Maltheren/Bilag-P2/Kicad filer/PowerAddOn/PowerAddOn/PowerAddOn2_Tekst.png

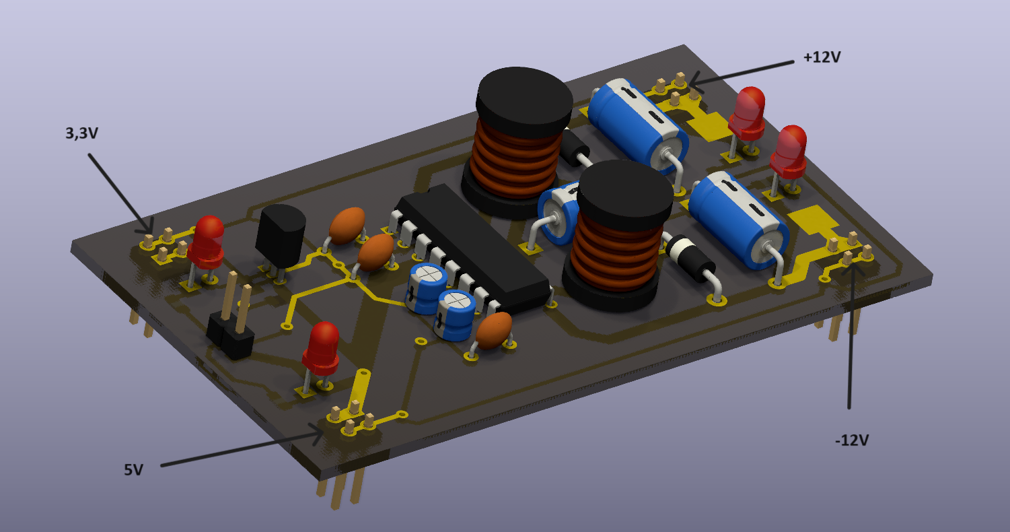
Kicad filer/PowerAddOn/PowerAddOn/PowerAddOn2_Tekst.png
