Maltheren/Bilag-P2/Kicad filer/PowerAddOn/PowerAddOn/PowerAddOn.png

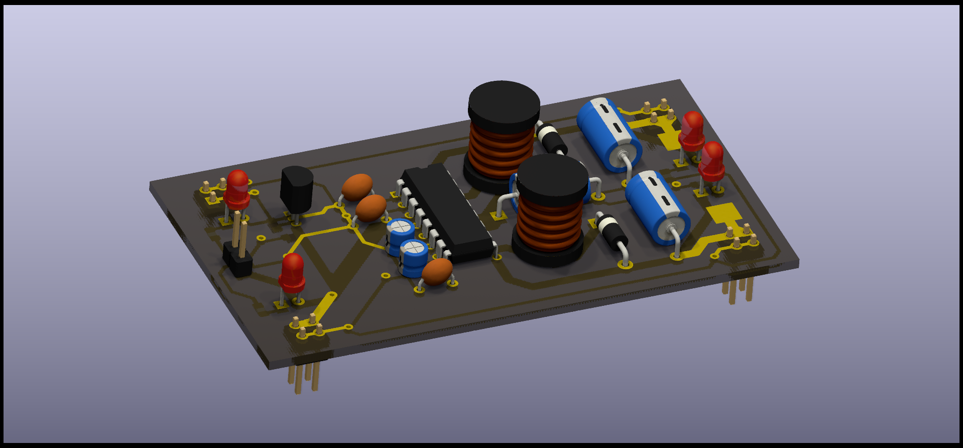
Kicad filer/PowerAddOn/PowerAddOn/PowerAddOn.png
