Maltheren/Bilag-P2/Kicad filer/PowerAddOn/PowerAddOn/PowerAddOn2.png

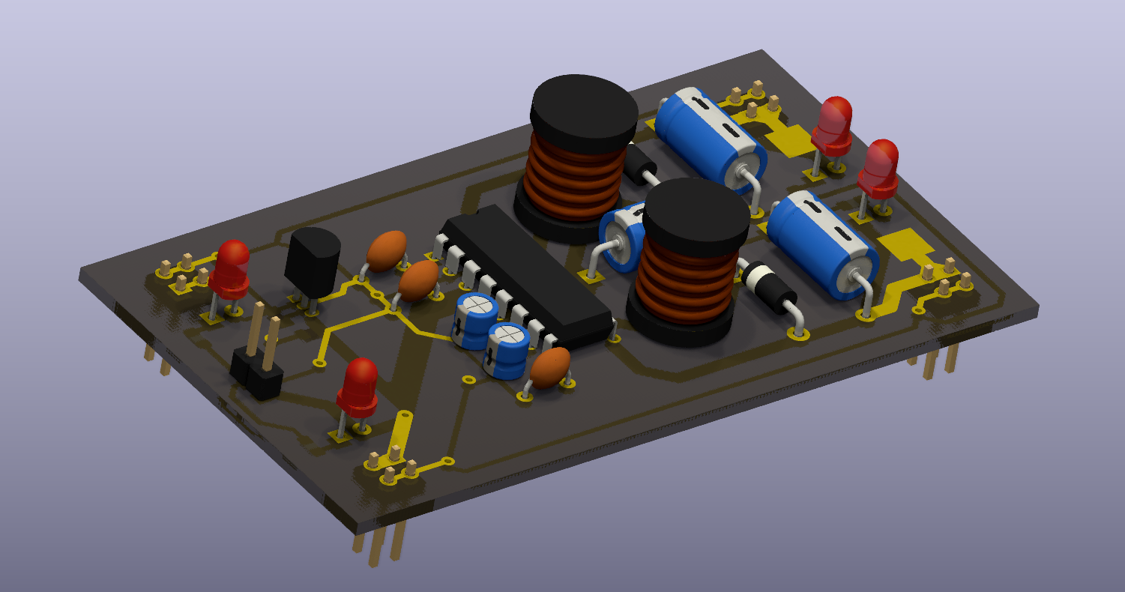
Kicad filer/PowerAddOn/PowerAddOn/PowerAddOn2.png
