Maltheren/Bilag-P2/Tests/Begge/S1 S2.csv

Frequency Log(Hz) | Gain (dB) | Phase (deg)
1.00010441154522 | -11.9575951670941 | -29.9110186335
1.02002096711708 | -10.968262479137 | -37.6873173948769
1.03995038360925 | -10.0583694415668 | -44.9132000611182
1.05985181982658 | -9.16374958422632 | -51.8982732066077
1.08009364755968 | -8.27616093757128 | -59.1885787538964
1.09981976674463 | -7.56683191751845 | -66.9312181141257
1.12016338353543 | -6.65872667450061 | -75.1817526079267
1.13994833382499 | -5.97810641974102 | -82.8378422791133
1.1598799011097 | -5.09345173903778 | -91.2556940941279
1.17990004057843 | -4.46642739230852 | -99.6509263969125
1.19995760707635 | -3.64138312726642 | -108.965429424205
1.22000782988254 | -3.14439374611364 | -117.749297890516
1.24001176959216 | -2.44859818749582 | -126.62713030138
1.25993577678249 | -1.8193012226693 | -136.34132482091
1.28000575955782 | -1.35183178602616 | -145.551987054429
1.29991959667752 | -0.882729519863348 | -155.262735367523
1.31989067760814 | -0.368316962118926 | -164.963904290659
1.34009406369643 | 0.000163560611546199 | -175.029001340476
1.36003523728506 | 0.295980291337435 | 175.345707751371
1.37991109385924 | 0.604438499301783 | 165.078606791357
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
