Maltheren/Bilag-P2/Tests/Begge/HelhedstestOpstilling.drawio.png

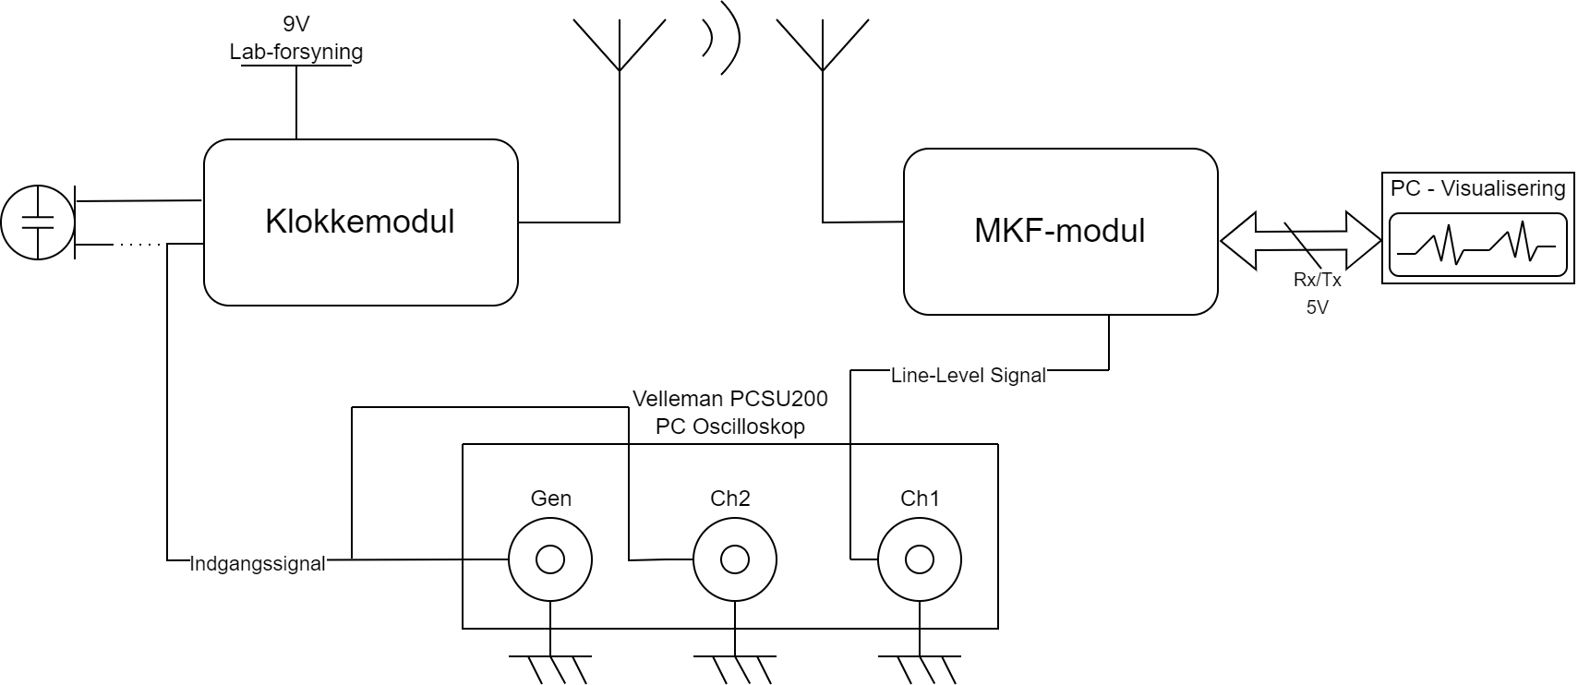
Tests/Begge/HelhedstestOpstilling.drawio.png
