Maltheren/Bilag-P2/Tests/Begge/HelhedstestOpstilling.png

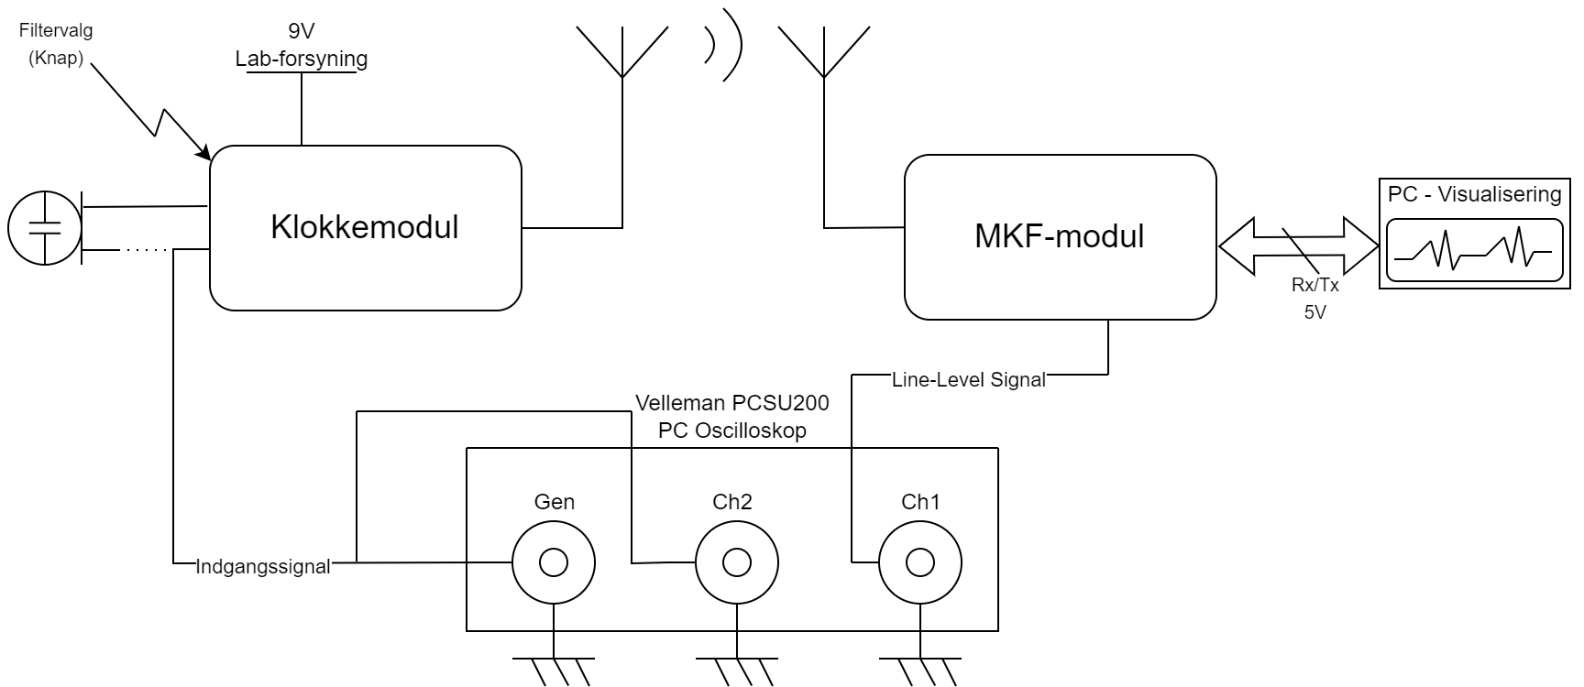
Tests/Begge/HelhedstestOpstilling.png
