Maltheren/Bilag-P2/Tests/Begge/Matlab/KlokkeOgRekon/Amplitude respons gengivelse.png

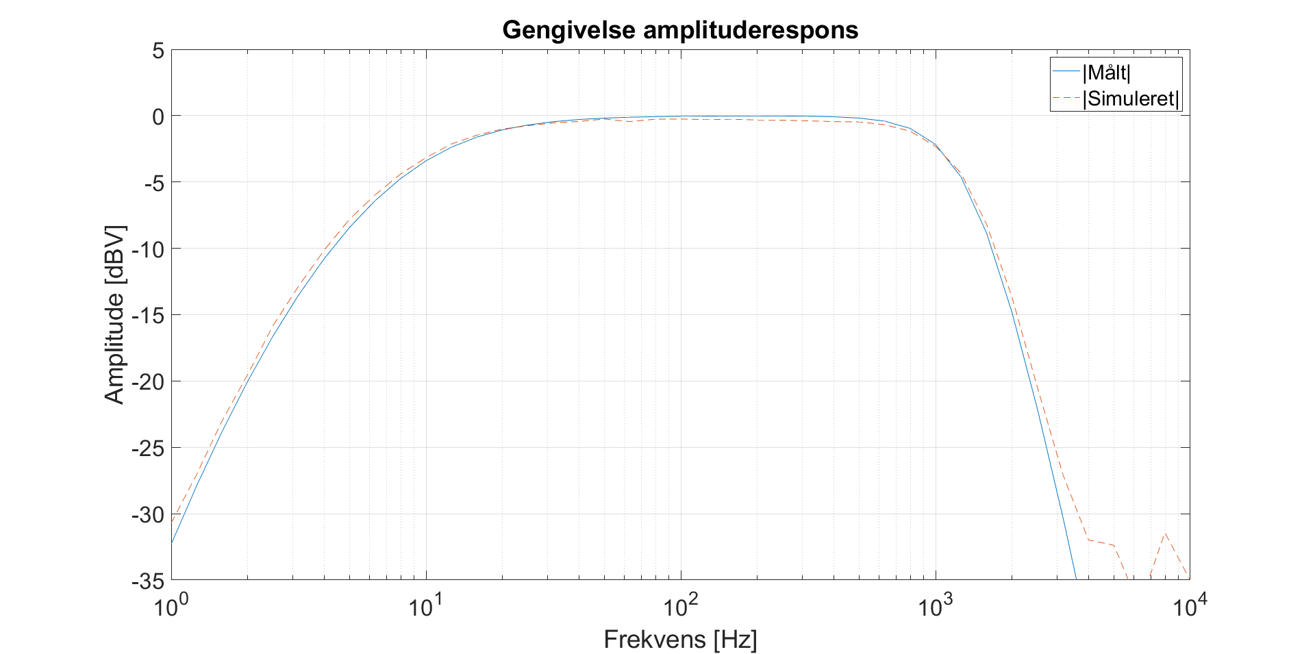
Tests/Begge/Matlab/KlokkeOgRekon/Amplitude respons gengivelse.png
