Maltheren/Bilag-P2/Tests/Begge/Matlab/KlokkeOgRekon/KlokkeOgRekon.jpg

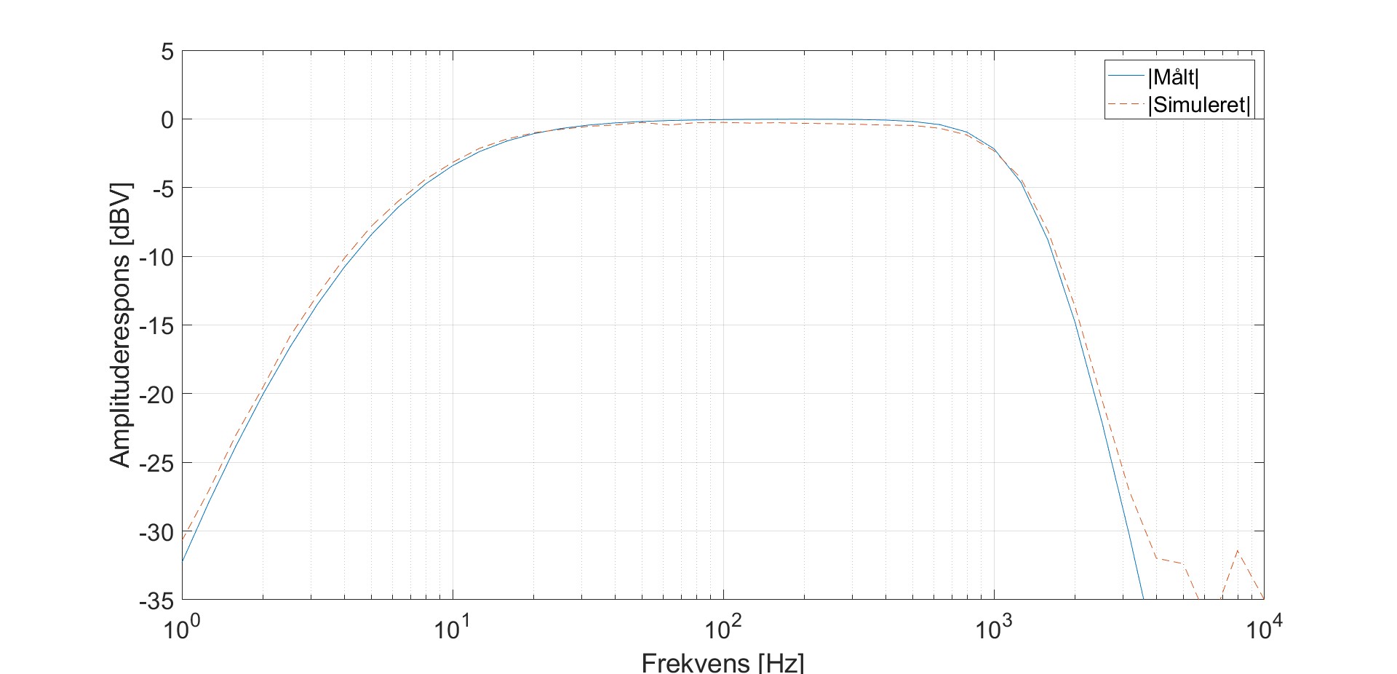
Tests/Begge/Matlab/KlokkeOgRekon/KlokkeOgRekon.jpg
