Maltheren/Bilag-P2/Tests/Begge/Matlab/Kvantisering/Billeder/Amplitude.png

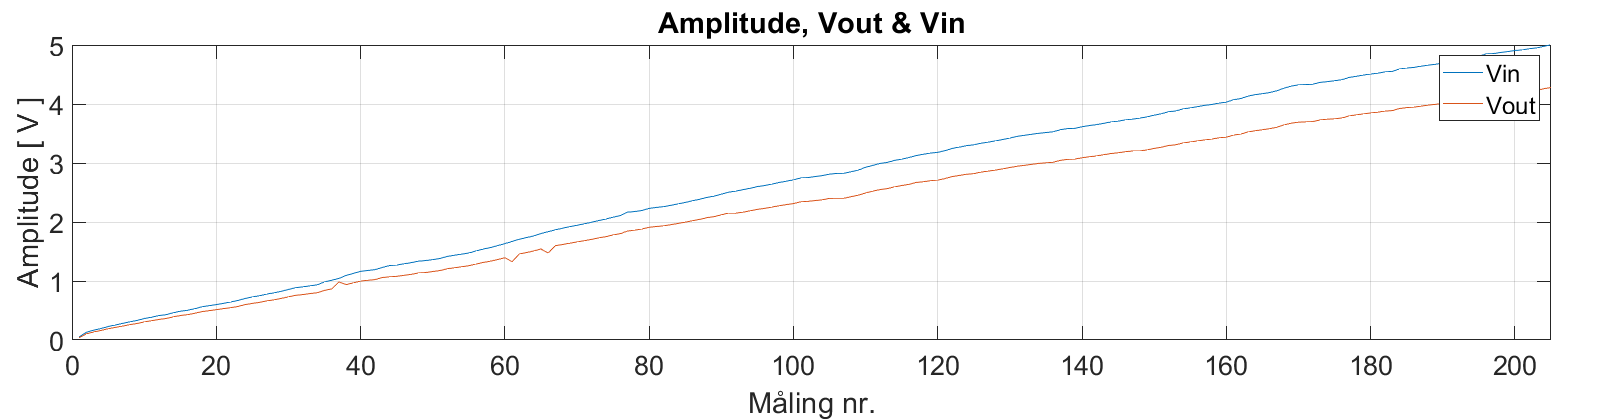
Tests/Begge/Matlab/Kvantisering/Billeder/Amplitude.png
