Maltheren/Bilag-P2/Tests/Begge/Matlab/Kvantisering/Billeder/Amplitude_VoutVin.jpg

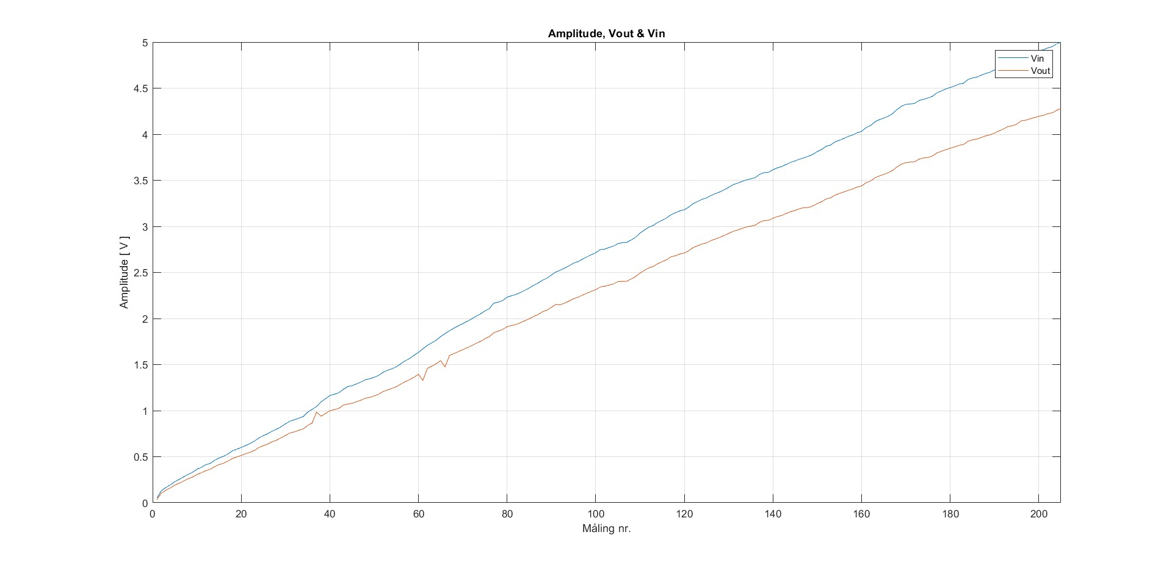
Tests/Begge/Matlab/Kvantisering/Billeder/Amplitude_VoutVin.jpg
