Maltheren/Bilag-P2/Tests/Begge/Matlab/Kvantisering/Billeder/Kvantiseringsfejl_Amplitude.jpg

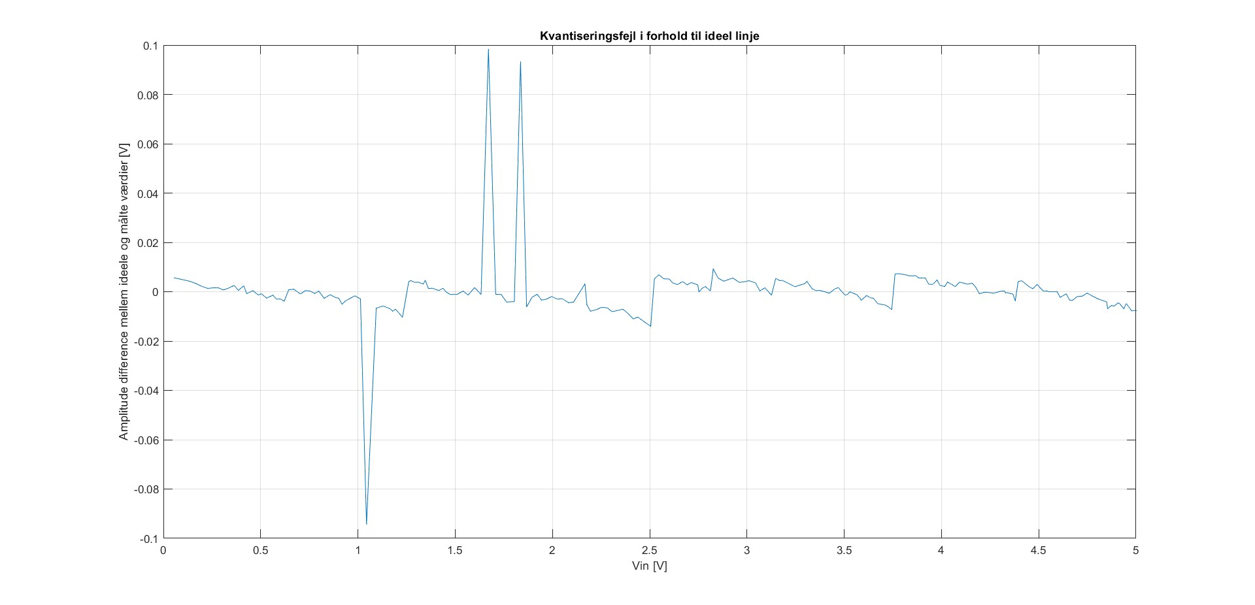
Tests/Begge/Matlab/Kvantisering/Billeder/Kvantiseringsfejl_Amplitude.jpg
