Maltheren/Bilag-P2/Tests/Begge/Matlab/Kvantisering/Billeder/Kvantiseringsfejl_ideel.png

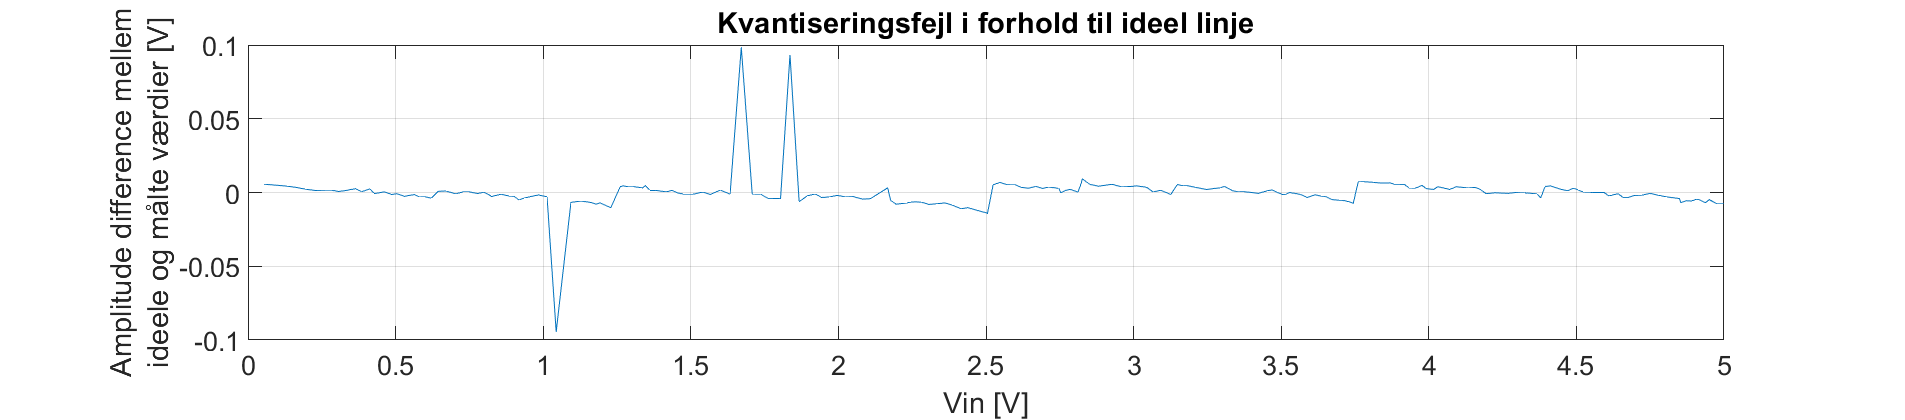
Tests/Begge/Matlab/Kvantisering/Billeder/Kvantiseringsfejl_ideel.png
