Maltheren/Bilag-P2/Tests/Begge/Matlab/Kvantisering/VinVout.jpg

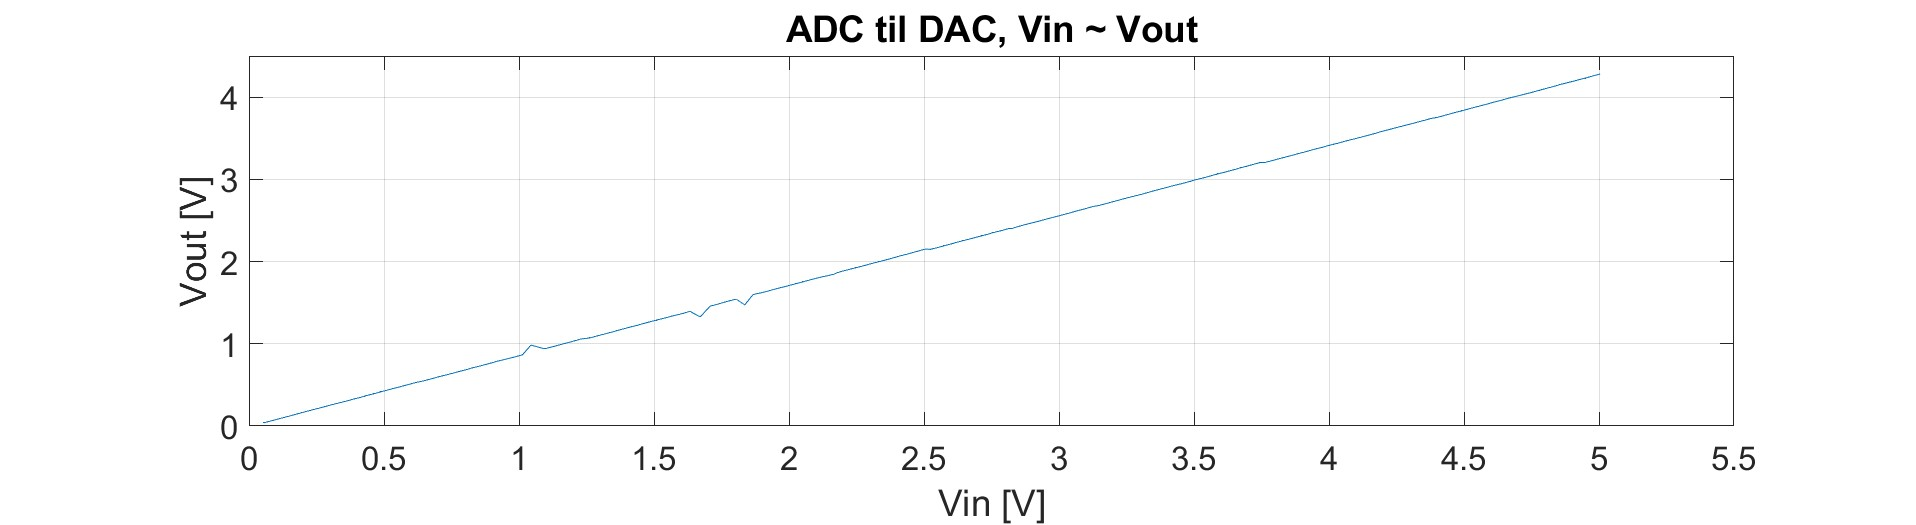
Tests/Begge/Matlab/Kvantisering/VinVout.jpg
