Maltheren/Bilag-P2/Tests/Begge/Matlab/SamletSystem/SamletH.jpg

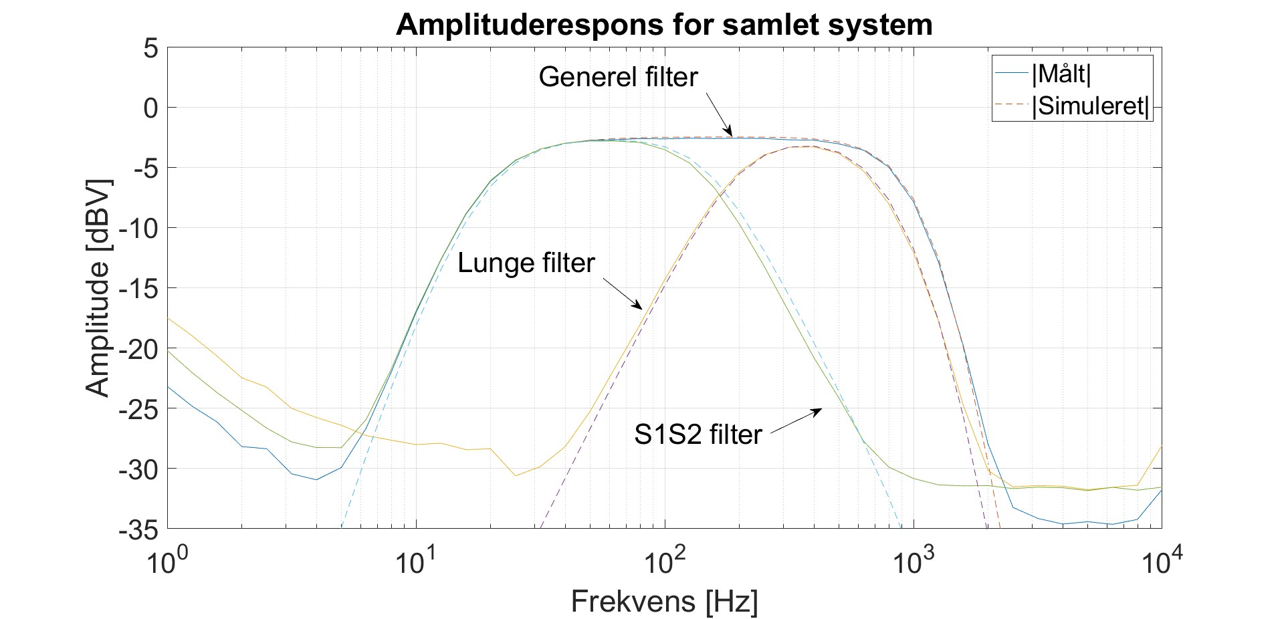
Tests/Begge/Matlab/SamletSystem/SamletH.jpg
