Maltheren/Bilag-P2/Tests/Klokke/Gain/Plot_AGC_Matlab.jpg

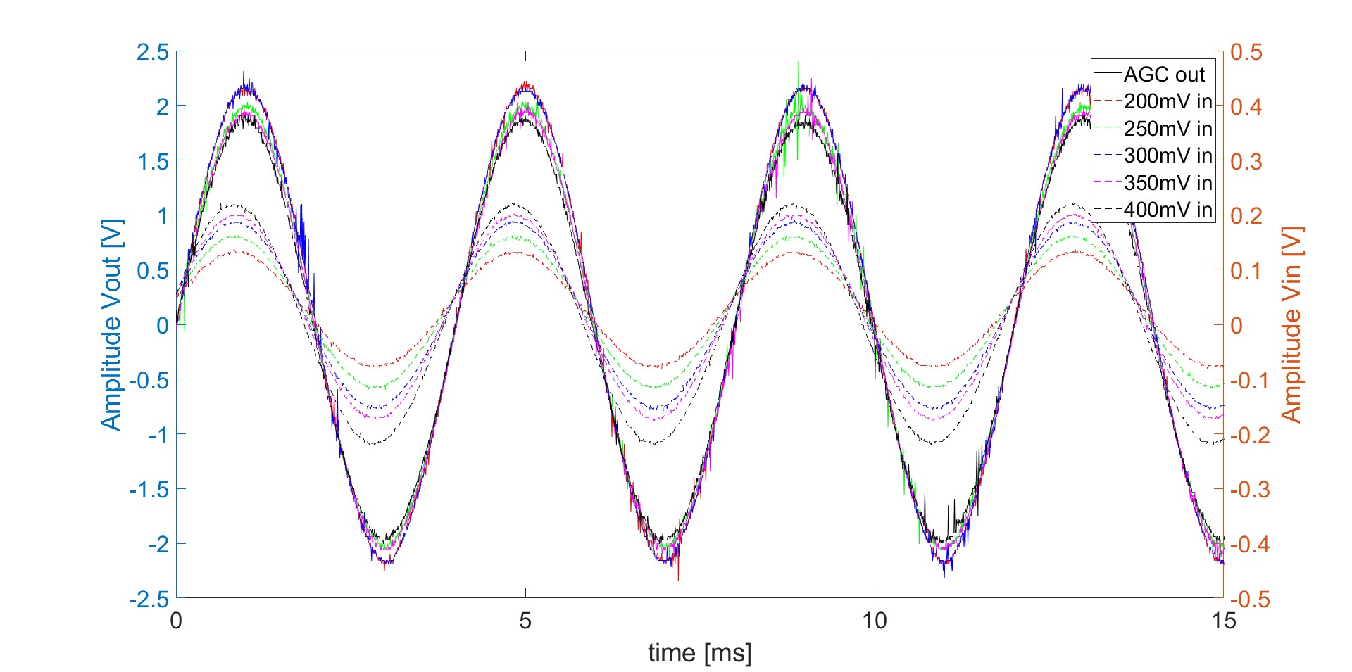
Tests/Klokke/Gain/Plot_AGC_Matlab.jpg
