Maltheren/Bilag-P2/Tests/MKF/Frekvensrespons/GenerelleFilter.jpg

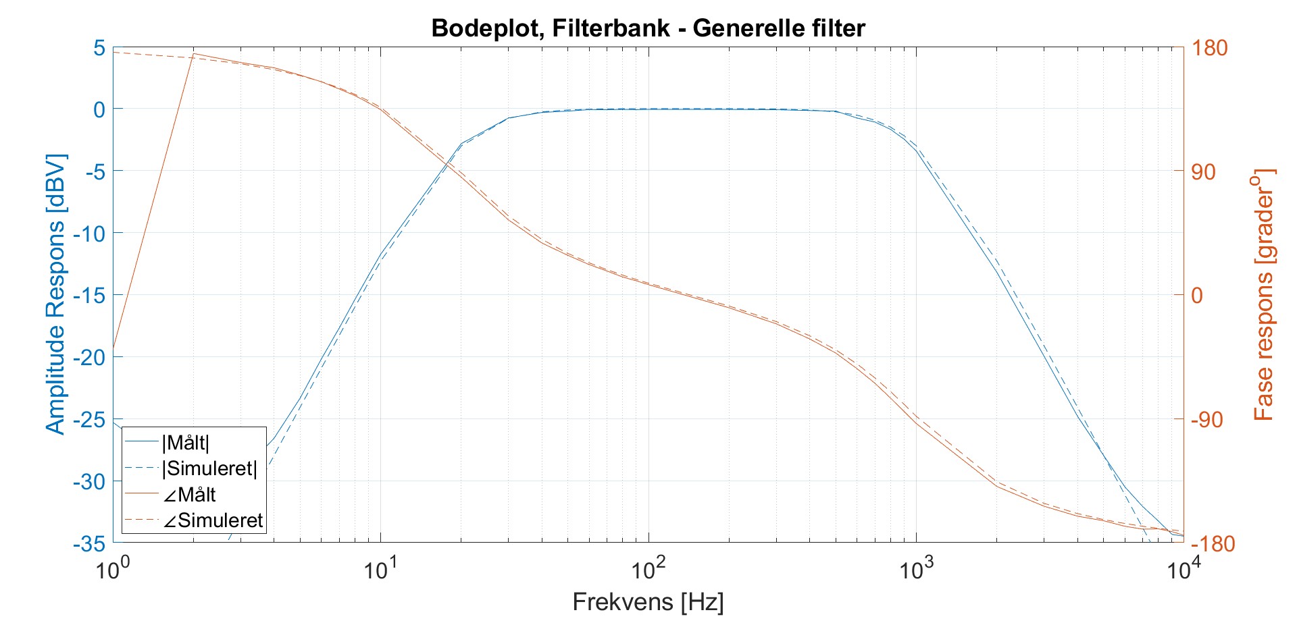
Tests/MKF/Frekvensrespons/GenerelleFilter.jpg
