Maltheren/Bilag-P2/Tests/MKF/Frekvensrespons/RekonFilter.jpg

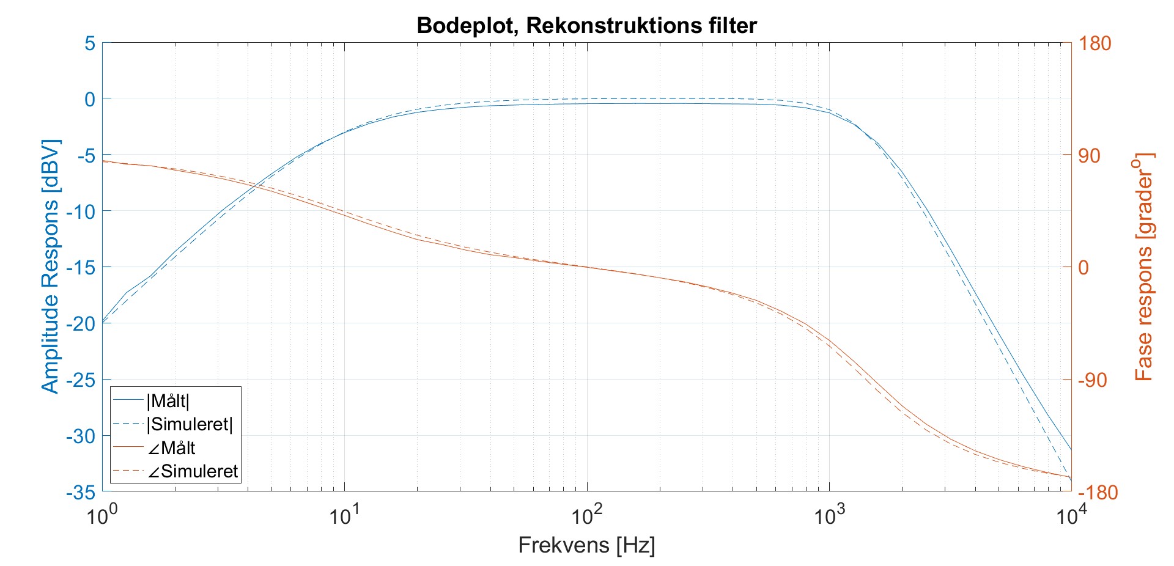
Tests/MKF/Frekvensrespons/RekonFilter.jpg
