Maltheren/Bilag-P2/Tests/MKF/Frekvensrespons/S1S2Filter.jpg

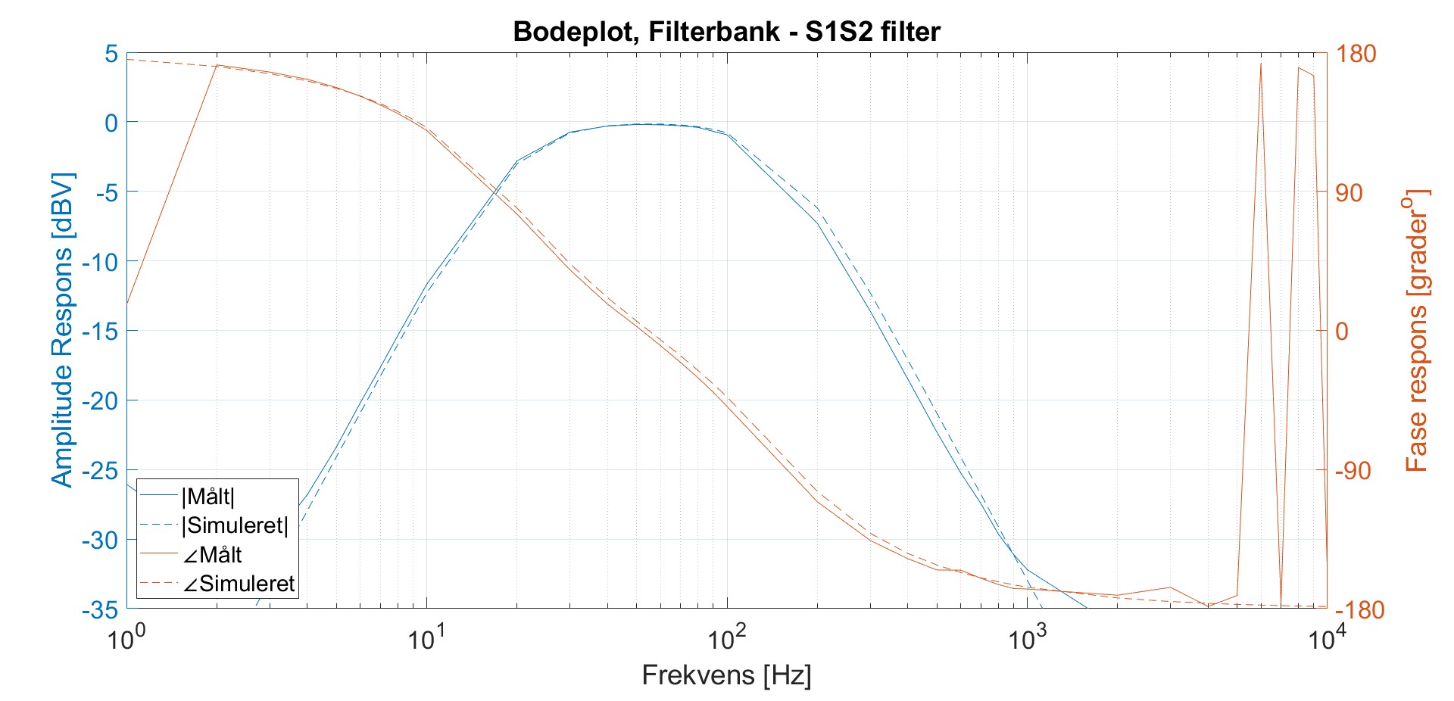
Tests/MKF/Frekvensrespons/S1S2Filter.jpg
