Maltheren/Bilag-P2/Tests/MKF/MKF_Filtrer_Overføring.jpg

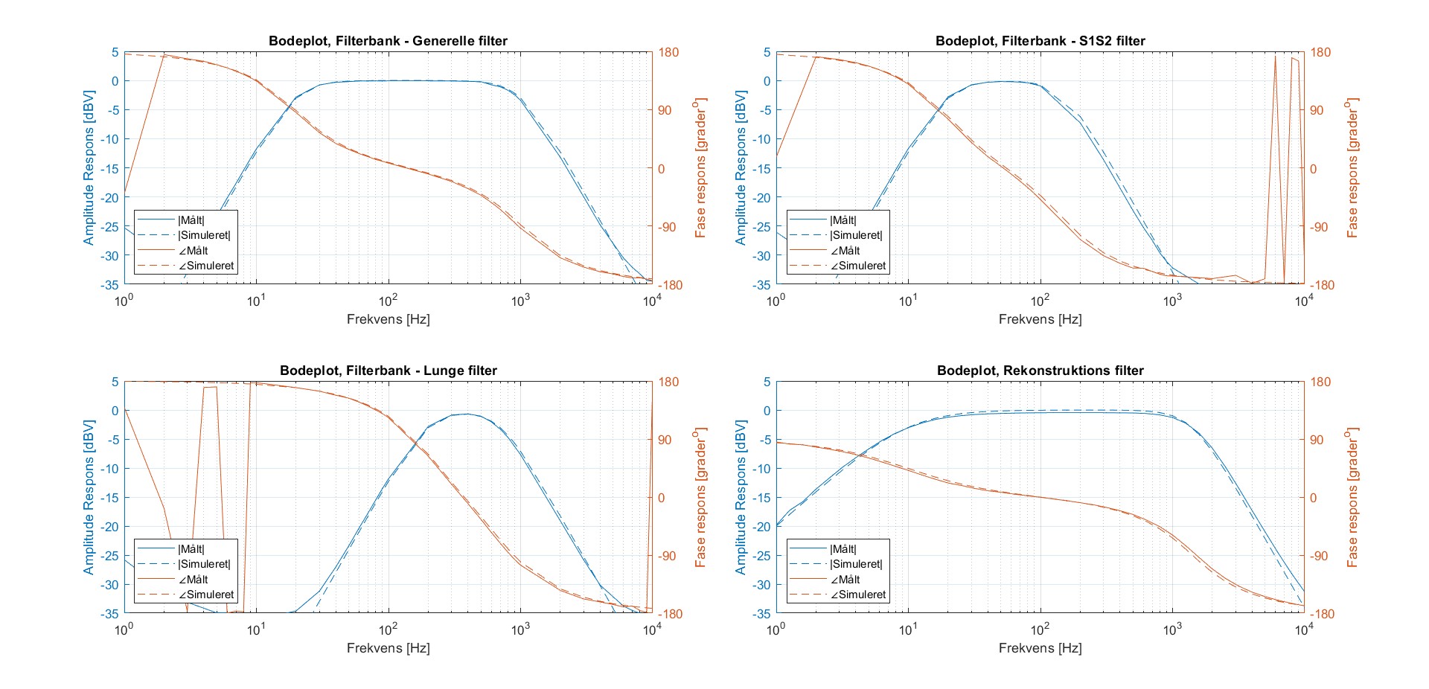
Tests/MKF/MKF_Filtrer_Overføring.jpg
