Maltheren/Bilag-P2/Tests/Klokke/Klokke efter fix/Fucking fixede anti aliasing.png

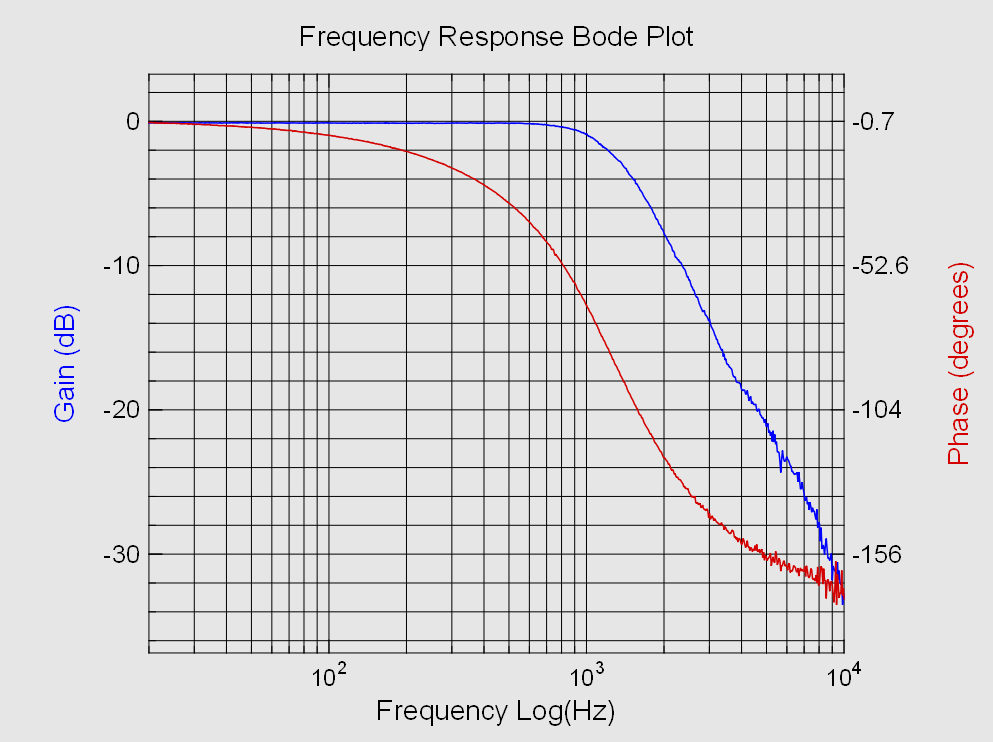
Tests/Klokke/Klokke efter fix/Fucking fixede anti aliasing.png
